HackerSchool/pico-synth/src/HardwareManager.hpp

#ifndef HARDWARE_MANAGER
#define HARDWARE_MANAGER

#include "Synth.hpp"
#include "Wavetable.hpp"
#include "hardware/i2c.h"
#include "hardware/pio.h"
#include "Sampler.hpp"
// #include "i2s_init.hpp"
#include "quadrature_encoder.pio.h"
#include "ssd1306.h"
#include "tusb.h"
#include <cstddef>
#include <cstdint>

#define PCF8574_KEYPAD_ADDR 0x20
#define PCF8574_LED_ADDR_1 0x20
#define PCF8574_LED_ADDR_2 0x21
#define NUM_ENCODERS 4

// Struct for each encoder's runtime state
typedef struct {
    int32_t last_count;
    uint clk_pin;
    uint sw_pin;
    PIO pio;
    uint sm;

    int32_t delta;
    bool button_state;
    bool button_edge;

} Encoder;

struct KeyChanges {
    uint16_t note_on_mask;
    uint16_t note_off_mask;
};

KeyChanges compute_key_changes(uint16_t prev_state, uint16_t curr_state);

extern Encoder encoders[NUM_ENCODERS];

// Initialize a quadrature encoder PIO state machine
void init_encoder(Encoder *enc);

// Get count from the encoder
// inline int32_t get_encoder_count(PIO pio, uint sm);

uint16_t scan_key_state(i2c_inst_t *i2c);

void update_led(i2c_inst_t *i2c, int key, bool on);

void update_leds_from_keys(i2c_inst_t *i2c, uint16_t prev_state,
                           uint16_t curr_state);

class HardwareManager {
  public:
    HardwareManager();

    // Display
    ssd1306_t disp;

    void init();
    void update();      // called every loop
    void poll_inputs(); // handle encoders + buttons
    void update_display();

    Encoder encoders[NUM_ENCODERS] = {
        {.last_count = 0,
         .clk_pin = 10,
         .sw_pin = 9,
         .pio = pio0,
         .sm = 0,
         .delta = 0,
         .button_state = 0,
         .button_edge = 0},
        {.last_count = 0,
         .clk_pin = 7,
         .sw_pin = 6,
         .pio = pio0,
         .sm = 1,
         .delta = 0,
         .button_state = 0,
         .button_edge = 0},
        {.last_count = 0,
         .clk_pin = 4,
         .sw_pin = 3,
         .pio = pio0,
         .sm = 2,
         .delta = 0,
         .button_state = 0,
         .button_edge = 0},
        {.last_count = 0,
         .clk_pin = 1,
         .sw_pin = 0,
         .pio = pio0,
         .sm = 3,
         .delta = 0,
         .button_state = 0,
         .button_edge = 0},
    };

    // int current_adsr_param = 0; // 0=A, 1=D, 2=S, 3=R
    // bool adsr_dirty = 0;
    // bool filter_dirty = 0;

    uint16_t curr_switches = 0;

    void draw_notes();
    void draw_wave_type(uint8_t midi_channel, int8_t octave,
                        uint16_t waveform_phase = 0);
    void draw_adsr(int current_adsr_param, uint8_t a, uint8_t d, uint8_t s,
                   uint8_t r);
    void draw_midi_settings(bool midi_out, bool midi_in, bool switches_in,
                            bool sequencer_in, bool sequencer_out);
    void draw_filter(uint8_t filter_type, float cutoff);

    void draw_sequencer_settings(bool playing, uint32_t tempo,
                                 uint8_t current_step);

    void draw_sequencer_note_edit(uint8_t current_step, uint8_t midi_channel,
                                  bool auto_stepping_enabled, bool is_playing,
                                  uint8_t *step_notes, uint8_t *step_channels);

    void draw_fm_edit(uint8_t midi_channel, uint8_t selected_operator,
                      int8_t octave, uint8_t fm_edit_mode, WaveType wave_type,
                      uint8_t attack, uint8_t decay, uint8_t sustain,
                      uint8_t release, uint16_t ratio, uint16_t feedback,
                      uint16_t fm_depth);
    void draw_karplus_main(uint8_t midi_channel, int8_t octave,
                           KarplusImpulseType impulse_type,
                           uint8_t filter_gain, uint8_t decay,
                           uint8_t body_resonance,
                           uint8_t last_note, uint16_t delay_samples,
                           uint16_t waveform_phase = 0);
    void draw_karplus_edit(uint8_t midi_channel, int8_t octave,
                           uint8_t impulse_length, uint8_t pick_position,
                           uint8_t dispersion, uint8_t body_resonance,
                           uint8_t last_note, uint16_t delay_samples);
    void draw_modal_main(uint8_t midi_channel, int8_t octave,
                         uint8_t structure, uint8_t brightness,
                         uint8_t damping, uint8_t position,
                         ModalExciterType exciter_type, uint8_t last_note);
    void draw_modal_edit(uint8_t midi_channel, int8_t octave,
                         ModalExciterType exciter_type, uint8_t structure,
                         uint8_t brightness, uint8_t damping,
                         uint8_t position, uint8_t last_note);

    void draw_choose_menu(int chosen_index);
    void draw_bitmap_select_menu(const uint8_t *bitmap_data,
                                 std::size_t bitmap_size, const char *title);
    void draw_engine_select_menu(int chosen_index, int active_engine_index);

    void draw_sampler_menu(const WavFileList& wav_files, int sample_index, int sample_channel);

    void draw_fx_menu(int fx_id, bool enabled, int p1, int p2, int mix);
    void draw_analog_menu(bool enabled, uint16_t frequency_hundredths_hz,
                          uint16_t dispersion_hundredths_percent);
    void draw_lfo_menu(uint8_t selected_lfo, uint8_t total_lfos,
                       const char *engine_name, const char *route_name,
                       WaveType wave_type, uint16_t frequency_hundredths_hz,
                       uint16_t depth_hundredths_percent);

    void display_show();
    void display_clear();

  private:
    // Synth &synth;

    std::bitset<128> last_note_state;
    WaveType last_wave_type = static_cast<WaveType>(-1);

    // Helpers
    void poll_encoders();
    void poll_keypad();
    void update_leds(uint16_t prev, uint16_t curr);

    // uint16_t prev_state = 0;

    void init_display();
    // bool last_encoder1_button = true; // for edge detection
    // bool last_encoder2_button = true; // for edge detection
};

#endif // !HARDWARE_MANAGER
//
