HackerSchool/pico-synth/src/synth/Wavetable.cpp

#include "Wavetable.hpp"
#include "fixed_point.h"
#include "math.h"

const int16_t Q14_MAX = 16384;

const char *wave_type_to_string(WaveType type) {
    switch (type) {
    case Sine:
        return "Sine";
    case Square:
        return "Square";
    case Triangle:
        return "Triangle";
    case Sawtooth:
        return "Saw";
    case Sinc:
        return "Sinc";
    default:
        return "Unknown";
    }
}

// This method allows to define the wavetable at compile time!
// Sine Wavetable
const std::array<int16_t, WAVE_TABLE_LEN> sine_wave_table{[]() {
        std::array<int16_t, WAVE_TABLE_LEN> table{};
        for (int i = 0; i < WAVE_TABLE_LEN; i++) {
            table[i] = static_cast<int16_t>(32767 *
                                            sin(i * 2 * M_PI / WAVE_TABLE_LEN));
        }
        return table;
    }()};

const std::array<int16_t, WAVE_TABLE_LEN> cos_wave_table{[]() {
        std::array<int16_t, WAVE_TABLE_LEN> table{};
        for (int i = 0; i < WAVE_TABLE_LEN; i++) {
            table[i] = static_cast<int16_t>(32767 *
                                            cos(i * 2 * M_PI / WAVE_TABLE_LEN));
        }
        return table;
    }()};

// Sinc Wavetable N = 32
const std::array<int16_t, WAVE_TABLE_LEN> sinc_table{[]() {
        std::array<int16_t, WAVE_TABLE_LEN> table{};
        int N = 32; // Window size
        for (int i = 0; i < WAVE_TABLE_LEN; i++) {
            // Handle the special case at i=0 to avoid division by zero
            if (i == 0) {
                table[i] = static_cast<int16_t>(
                    32767); // sinc(0) = 1, scaled to int16_t range
            } else {
                double x = static_cast<double>(i) / N;
                table[i] =
                    static_cast<int16_t>(32767 * sin(M_PI * x) / (M_PI * x));
            }
        }
        return table;
    }()};

// Square Wavetable
const std::array<int16_t, WAVE_TABLE_LEN> square_wave_table{[]() {
        std::array<int16_t, WAVE_TABLE_LEN> table{};
        for (int i = 0; i < WAVE_TABLE_LEN; i++) {
            table[i] = (i < WAVE_TABLE_LEN / 2) ? 32767 : -32767;
        }
        return table;
    }()};

// Triangle Wavetable
const std::array<int16_t, WAVE_TABLE_LEN> triangle_wave_table{[]() {
        std::array<int16_t, WAVE_TABLE_LEN> table{};
        for (int i = 0; i < WAVE_TABLE_LEN; i++) {
            float phase = static_cast<float>(i) / WAVE_TABLE_LEN;
            if (phase < 0.5f) {
                table[i] = static_cast<int16_t>(4 * 32767 * phase - 32767);
            } else {
                table[i] =
                    static_cast<int16_t>(-4 * 32767 * (phase - 0.5f) + 32767);
            }
        }
        return table;
    }()};

// Sawtooth Wavetable
const std::array<int16_t, WAVE_TABLE_LEN> sawtooth_wave_table{[]() {
        std::array<int16_t, WAVE_TABLE_LEN> table{};
        for (int i = 0; i < WAVE_TABLE_LEN; i++) {
            float phase = static_cast<float>(i) / WAVE_TABLE_LEN;
            table[i] = static_cast<int16_t>(2 * 32767 * phase - 32767);
        }
        return table;
    }()};

// Sinc Wavetable N = 32
const std::array<q8_24_t, WAVE_TABLE_LEN> sinc_table_fp{[]() {
    std::array<q8_24_t, WAVE_TABLE_LEN> table{};
    int N = 32; // Window size
    for (int i = 0; i < WAVE_TABLE_LEN; i++) {
        // Handle the special case at i=0 to avoid division by zero
        if (i == 0) {
            table[i] = Q24_ONE; // sinc(0) = 1, scaled to int16_t range
        } else {
            double x = (static_cast<double>(i) * N) / WAVE_TABLE_LEN;
            table[i] = q24_from_float(
                static_cast<float>((sin(M_PI * x) / (M_PI * x))));
        }
    }
    return table;
}()};

// Hanning Window Wavetable N = 32
const std::array<q8_24_t, FILTER_ORDER> hanning_window_table_fp{[]() {
    std::array<q8_24_t, FILTER_ORDER> table{};
    for (int i = 0; i < FILTER_ORDER; i++) {
        // Hanning window formula: 0.5 * (1 - cos(2π*n/(N-1)))
        double value =
            0.5 * (1.0 - cos((2.0 * M_PI * i) / (FILTER_ORDER - 1.0)));
        table[i] = q24_from_float(value); // Scale to int16_t range
    }
    return table;
}()};

const std::array<int16_t, WAVE_TABLE_LEN> tan_wave_table{[]() {
    std::array<int16_t, WAVE_TABLE_LEN> table{};
    for (int i = 0; i < WAVE_TABLE_LEN; i++) {
        table[i] = static_cast<int16_t>(
            32767 * tan(i * 0.25 * M_PI /
                        WAVE_TABLE_LEN)); // in this range it goes from 0 to 1
    }
    return table;
}()};

// Lookup tables for sinh, cosh, and u approximations
const std::array<int16_t, WAVE_TABLE_LEN> sinh_wave_table{[]() {
    std::array<int16_t, WAVE_TABLE_LEN> table{};
    for (int i = 0; i < WAVE_TABLE_LEN; i++) {
        double x = (1.0 * i / WAVE_TABLE_LEN); // Range (0,1]
        table[i] = static_cast<int16_t>(Q14_MAX * sinh(x));
    }
    return table;
}()};

const std::array<int16_t, WAVE_TABLE_LEN> cosh_wave_table{[]() {
    std::array<int16_t, WAVE_TABLE_LEN> table{};
    for (int i = 0; i < WAVE_TABLE_LEN; i++) {
        double x = (1.0 * i / WAVE_TABLE_LEN);
        table[i] = static_cast<int16_t>(Q14_MAX * cosh(x));
    }
    return table;
}()};

const std::array<int16_t, WAVE_TABLE_LEN> u_wave_table{[]() {
    std::array<int16_t, WAVE_TABLE_LEN> table{};
    for (int i = 1; i < WAVE_TABLE_LEN; i++) { // Start at 1 to avoid log(0)
        double x = (1.0 * i / WAVE_TABLE_LEN); // Range (0,1]
        table[i] =
            static_cast<int16_t>(Q14_MAX * log((1.0 + sqrt(1.0 + x * x)) / x));
    }
    table[0] = table[1]; // Avoid issues with index 0
    return table;
}()};

const std::array<uint32_t, 128> adsr_curve_table{[]() {
        std::array<uint32_t, 128> table{};
        
        // Tuning parameters - adjust these easily
        const float min_time = 0.001f;  
        const float max_time = 25.0f; 
        const float curve_steepness = 0.05f;  // Higher = more steep curve
        
        for (int i = 0; i < 128; i++) {
            if (i == 0) {
                table[i] = (32768UL << 16) / 100; // Special case for instant
            } else {
                float normalized = (127 - i) / 127.0f; // 0.0 to 1.0, flipped
                
                // Reciprocal curve: 1/(1 + steepness*(1-x))
                float curve_factor = 1.0f / (1.0f + curve_steepness * (1.0f - normalized));
                
                // Map to time range
                float time_seconds = min_time + (max_time - min_time) * (1.0f - curve_factor);
                
                // Calculate increment
                float increment_float = (32768UL << 16) / (time_seconds * 44100.0f);
                uint32_t increment = static_cast<uint32_t>(increment_float);
                table[i] = increment > 0 ? increment : 1;
            }
        }
        return table;
    }()};
