HackerSchool/pico-synth/src/synth/Wavetable.hpp

#ifndef WAVETABLE
#define WAVETABLE

#include "fixed_point.h"
#include <array>
#include <cstdint>

#define WAVE_TABLE_LEN 2048
#define FILTER_ORDER 33

#define WAVE_SHIFT 11
#define WAVE_LEN 2048
#define WAVE_MAX 0x8000000

enum WaveType { Sine, Square, Triangle, Sawtooth, Sinc };

const char *wave_type_to_string(WaveType type);

extern const std::array<int16_t, WAVE_TABLE_LEN> sine_wave_table;
extern const std::array<int16_t, WAVE_TABLE_LEN> square_wave_table;
extern const std::array<int16_t, WAVE_TABLE_LEN> triangle_wave_table;
extern const std::array<int16_t, WAVE_TABLE_LEN> sawtooth_wave_table;
extern const std::array<int16_t, WAVE_TABLE_LEN> sinc_table;

extern const std::array<int16_t, WAVE_TABLE_LEN> cos_wave_table;
extern const std::array<int16_t, WAVE_TABLE_LEN> tan_wave_table;
extern const std::array<int16_t, WAVE_TABLE_LEN> cosh_wave_table;
extern const std::array<int16_t, WAVE_TABLE_LEN> sinh_wave_table;
extern const std::array<int16_t, WAVE_TABLE_LEN> u_wave_table;

extern const std::array<q8_24_t, WAVE_TABLE_LEN> sinc_table_fp;
extern const std::array<q8_24_t, FILTER_ORDER> hanning_window_table_fp;

extern const std::array<uint32_t, 128> adsr_curve_table;

#endif // !WAVETABLE
