HackerSchool/pico-synth/src/ui/choose_menu.cpp

#include "HardwareManager.hpp"
#include "Ui.hpp"

namespace {
inline int abs_int(int value) {
    return value < 0 ? -value : value;
}

constexpr UiState kVisibleChooseStates[] = {
    UI_STATE_MAIN,
    UI_STATE_FX_EDIT,
    UI_STATE_ANALOG,
    UI_STATE_LFO,
    UI_STATE_MIDI_SETTINGS,
    UI_STATE_SEQUENCER,
    UI_STATE_SAMPLER,
};

constexpr int kVisibleChooseStateCount =
    static_cast<int>(sizeof(kVisibleChooseStates) / sizeof(kVisibleChooseStates[0]));

int find_visible_choose_index(int chosen_index) {
    for (int i = 0; i < kVisibleChooseStateCount; ++i) {
        if (static_cast<int>(kVisibleChooseStates[i]) == chosen_index) {
            return i;
        }
    }
    return 0;
}
} // namespace

static int32_t encoder_accumulator = 0;
const int detent_threshold = 4;  // Change based on your encoder resolution

void UiHandler::choose_handle_encoders(UiHandler &self) {
    HardwareManager &hw = self.hw;
    for (int i = 0; i < NUM_ENCODERS; ++i) {
        Encoder *enc = &hw.encoders[i];
        int32_t delta = enc->delta;

        // Handle encoder rotations (if needed for future features)
        if (UiHandler::encoder_moved(delta)) {
            switch (i) {
            case 0:
                // Could cycle through MIDI channels or other settings
                break;
            case 1:
                // Could adjust MIDI velocity or other parameters
                break;
            case 2:
                // Could adjust other MIDI settings
                break;
            case 3:
                encoder_accumulator += delta;

                if (abs_int(static_cast<int>(encoder_accumulator)) >=
                    detent_threshold) {
                    int dir = UiHandler::encoder_velocity_delta(encoder_accumulator, 1, 1, 2);
                    encoder_accumulator = 0; // Reset after handling

                    int visible_index =
                        find_visible_choose_index(self.chosen_index);
                    visible_index += dir;
                    if (visible_index >= kVisibleChooseStateCount) {
                        visible_index = kVisibleChooseStateCount - 1;
                    } else if (visible_index < 0) {
                        visible_index = 0;
                    }

                    self.chosen_index =
                        static_cast<int>(kVisibleChooseStates[visible_index]);
                    self.chosen_dirty = true;
                }
                break;
            }
        }

        // Handle button presses for toggling flags
        if (!enc->button_state && enc->button_edge) {
            switch (i) {
            case 0:
                //self.midi_out = !self.midi_out;
                //self.midi_settings_dirty = true;
                //printf("MIDI Out: %s\n", self.midi_out ? "ON" : "OFF");
                self.chosen_dirty = true;
                break;
            case 1:
                self.chosen_dirty = true;
                break;
            case 2:
                self.chosen_dirty = true;
                break;
            case 3:
                if (self.chosen_index == UI_STATE_MAIN) {
                    self.release_all_tracked_switch_notes();
                    self.engine_select_index =
                        static_cast<int>(self.synth.get_engine());
                    self.ui_state = UI_STATE_ENGINE_SELECT;
                    self.engine_select_dirty = true;
                } else {
                    self.release_all_tracked_switch_notes();
                    UiState target_state =
                        static_cast<UiState>(self.chosen_index);
                    if (self.chosen_index == UI_STATE_FM_EDIT &&
                        self.synth.get_engine() ==
                            SynthEngine::KarplusStrong) {
                        target_state = UI_STATE_MAIN;
                    } else if (self.chosen_index == UI_STATE_FM_EDIT &&
                               self.synth.get_engine() == SynthEngine::Modal) {
                        target_state = UI_STATE_MAIN;
                    }

                    self.ui_state = target_state;
                    self.chosen_dirty = true;
                    self.main_dirty = true;
                    self.adsr_dirty = true;
                    self.channel_dirty = true;
                    self.filter_dirty = true;
                    self.midi_settings_dirty = true;
                    self.sequencer_settings_dirty = true;
                    self.sequencer_dirty = true;
                    self.sampler_dirty = true;
                    self.fm_edit_dirty = true;
                    self.karplus_edit_dirty = true;
                    self.modal_edit_dirty = true;
                    self.lfo_dirty = true;
                    self.fx_dirty = true;
                    self.analog_dirty = true;
                }
                break;
            }
        }
    }
}

void UiHandler::choose_update_display(UiHandler &self) {
    if (self.preset_browse_overlay_active()) {
        return;
    }

    HardwareManager &hw = self.hw;

    if (self.chosen_dirty) {
        hw.draw_choose_menu(self.chosen_index);
        hw.display_show();
        self.chosen_dirty = false;
    }
}
