HackerSchool/pico-synth/src/ui/sampler_menu.cpp

#include "HardwareManager.hpp"
#include "Ui.hpp"

namespace {
const int key_to_midi[16] = {-1, 61, 63, -1, 60, 62, 64, 65,
                             66, 68, 70, -1, 67, 69, 71, 72};
} // namespace

void UiHandler::sampler_handle_encoders(UiHandler &self) {
    HardwareManager &hw = self.hw;
    for (int i = 0; i < NUM_ENCODERS; ++i) {
        Encoder *enc = &hw.encoders[i];
        int32_t delta = enc->delta;

        // Handle encoder rotations (if needed for future features)
        if (UiHandler::encoder_moved(delta)) {
            switch (i) {
            case 0:
                self.sampler_dirty = true;
                break;
            case 1:
                if (self.wav_files.get_count() > 0) {
                    int new_index = self.sample_index +
                                    UiHandler::encoder_velocity_delta(delta, 1, 2, 4);
                    const int file_count = self.wav_files.get_count();

                    while (new_index < 0) new_index += file_count;
                    while (new_index >= file_count) new_index -= file_count;

                    self.sample_index = new_index;
                }
                
                /*
                printf("WAV files count: %d\n", self.wav_files.get_count());
                if (self.wav_files.get_count() > 0) {
                    printf("Sample index: %d\n", self.sample_index);
                    printf("Sample: %s\n", self.wav_files.get_filename(self.sample_index).c_str());
                } else {
                    printf("No WAV files found!\n");
                }                
                */
                self.sampler_dirty = true;
                break;
            case 2:
                self.sampler_dirty = true;
                break;
            case 3:
                self.sampler_dirty = true;
                break;
            }
        }

        // Handle button presses for toggling flags
        if (!enc->button_state && enc->button_edge) {
            switch (i) {
            case 0:
                //self.midi_out = !self.midi_out;
                //self.midi_settings_dirty = true;
                //printf("MIDI Out: %s\n", self.midi_out ? "ON" : "OFF");
                self.sampler_dirty = true;
                break;
            case 1:
                self.sampler_dirty = true;
                break;
            case 2:
                self.sampler_dirty = true;
                break;
            case 3:
                // Exit back to main menu
                self.ui_state = UI_STATE_CHOOSE;
                self.chosen_index = UI_STATE_SAMPLER;
                self.sampler_dirty = true;
                self.chosen_dirty = true;
                break;
            }
        }
    }
}

void UiHandler::sampler_handle_switches(UiHandler &self) {
    const uint16_t curr = self.hw.curr_switches;
    KeyChanges changes = compute_key_changes(self.prev_switches, curr);
    update_leds_from_keys(i2c1, self.prev_switches, curr);

    for (int i = 0; i < 16; ++i) {
        if ((changes.note_on_mask >> i) & 1) {
            const int note = key_to_midi[i];
            if (note == 255) {
                continue;
            }

            const int player_id = note - 60;
            if (player_id >= 0 &&
                player_id < static_cast<int>(self.sampler.get_num_players())) {
                self.sampler.trigger_player(static_cast<uint8_t>(player_id));
            }
        }
    }

    self.prev_switches = curr;
}

void UiHandler::sampler_update_display(UiHandler &self) {
    if (self.preset_browse_overlay_active()) {
        return;
    }

    HardwareManager &hw = self.hw;

    if (self.sampler_dirty) {
        hw.draw_sampler_menu(self.wav_files, self.sample_index, self.sample_channel);
        hw.display_show();
        self.sampler_dirty = false;
    }
}
